aitesam961/electrivity/docs/image_2024-02-22_001135263.png

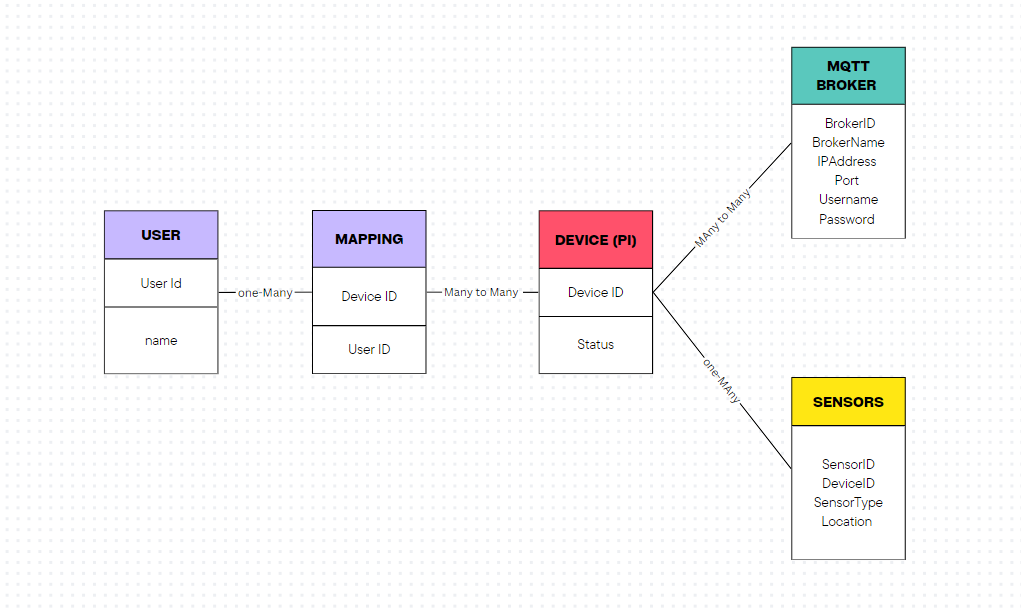
docs/image_2024-02-22_001135263.png
