aitesam961/electrivity/docs/images/image1.jpeg

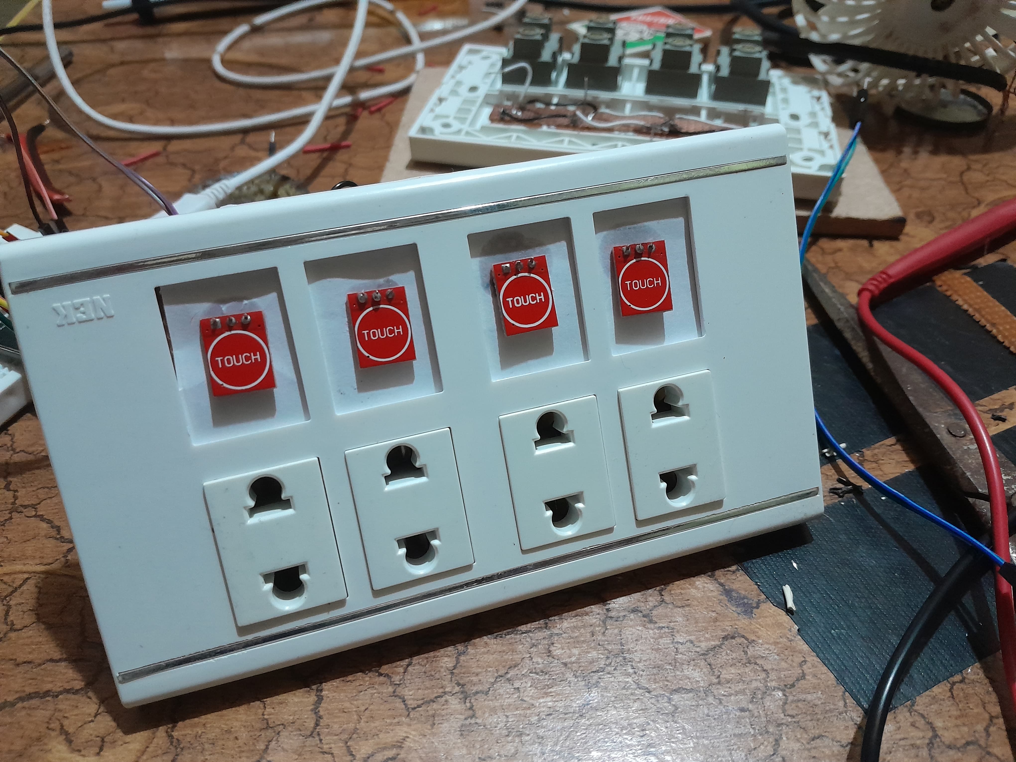
docs/images/image1.jpeg
