aitesam961/electrivity/docs/images/image2.jpeg

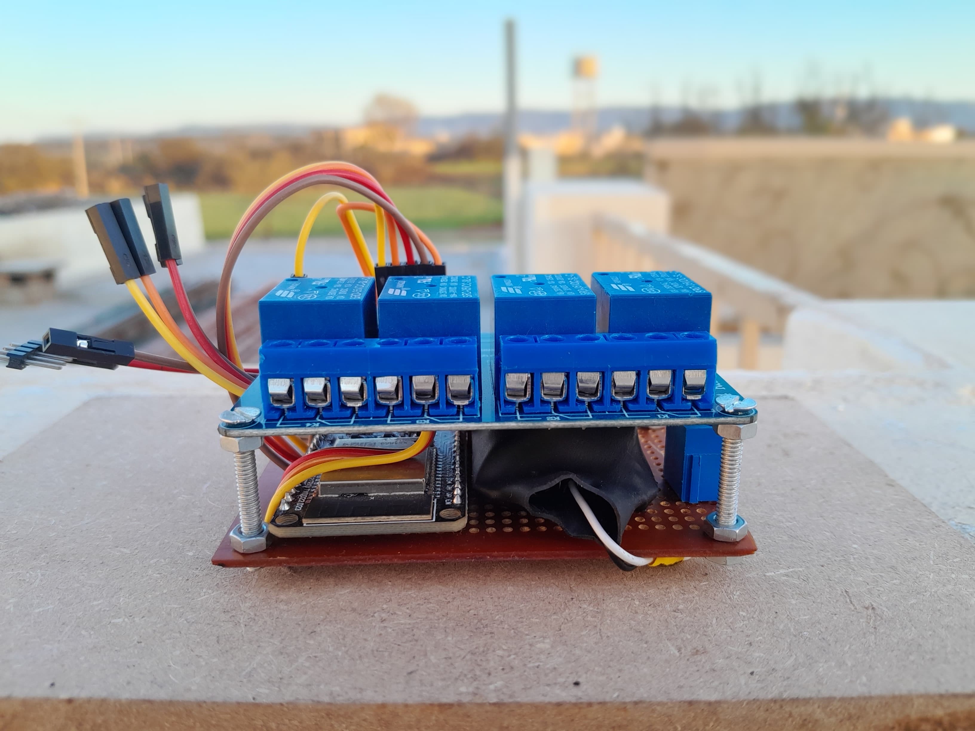
docs/images/image2.jpeg
