aitesam961/electrivity/docs/images/image3.jpeg

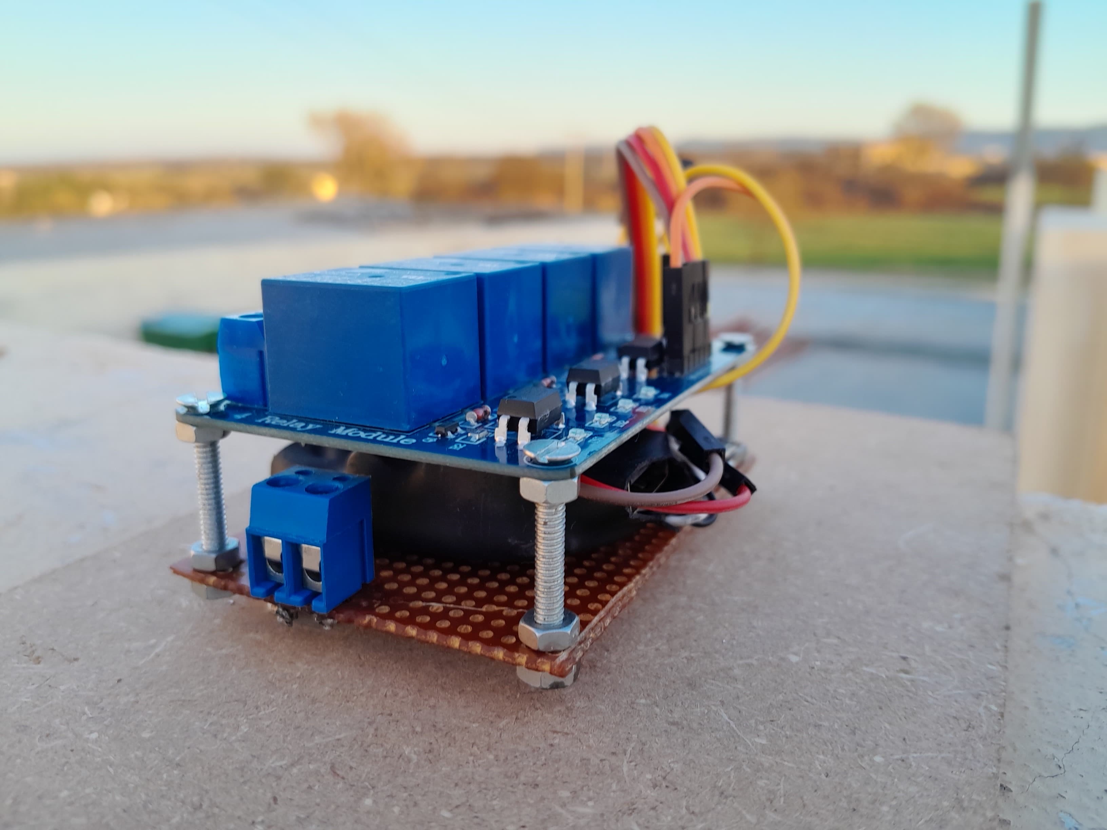
docs/images/image3.jpeg
