aitesam961/electrivity/docs/images/image4.jpeg

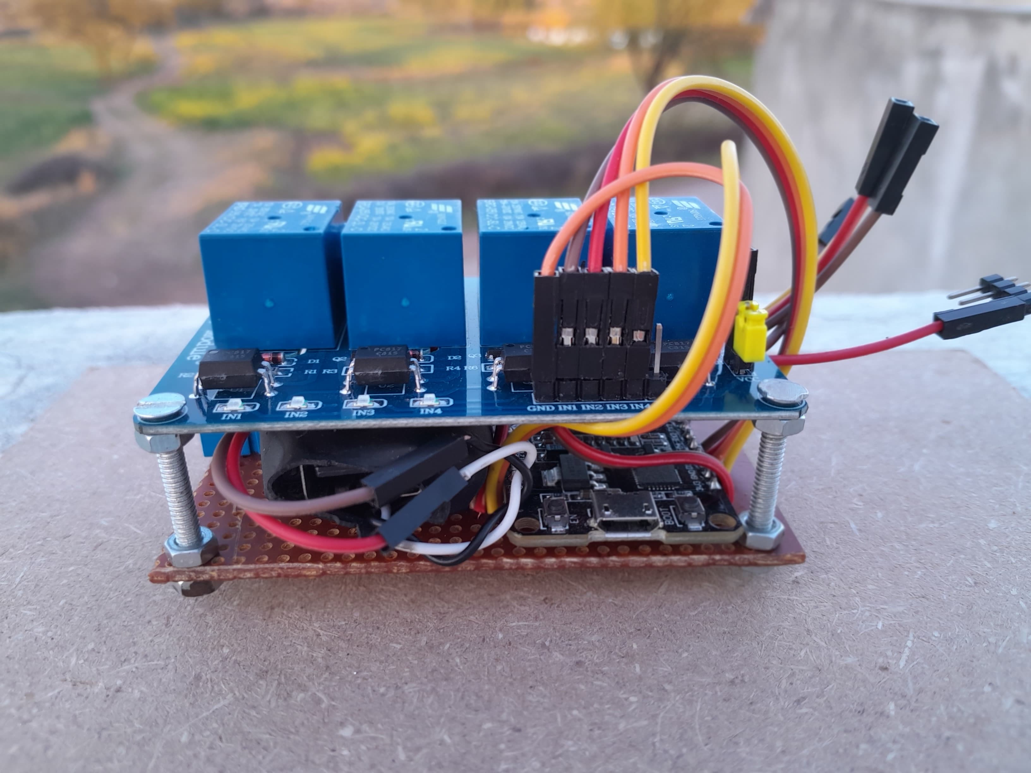
docs/images/image4.jpeg
