aitesam961/electrivity/docs/images/image5.jpeg

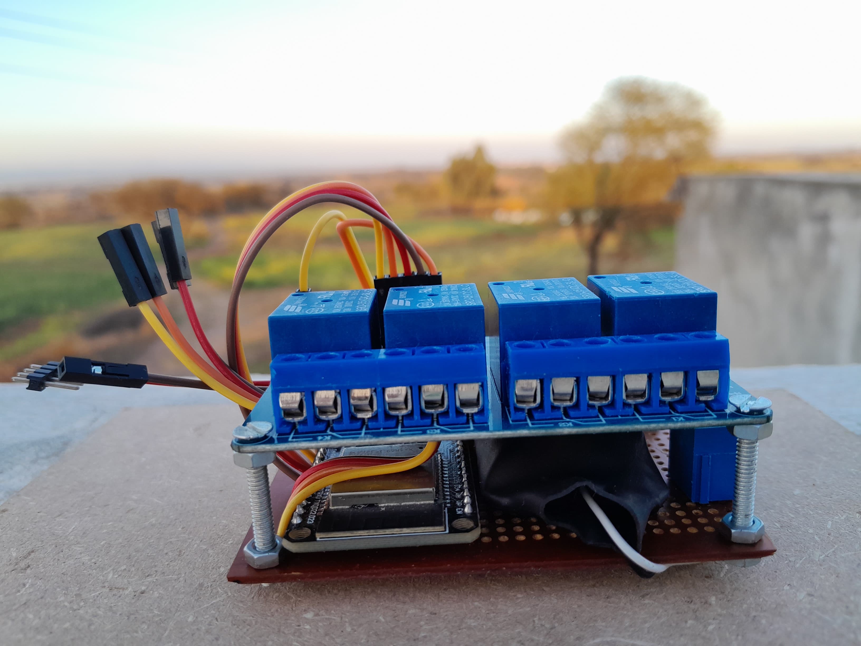
docs/images/image5.jpeg
