aitesam961/electrivity/docs/images/image6.jpeg

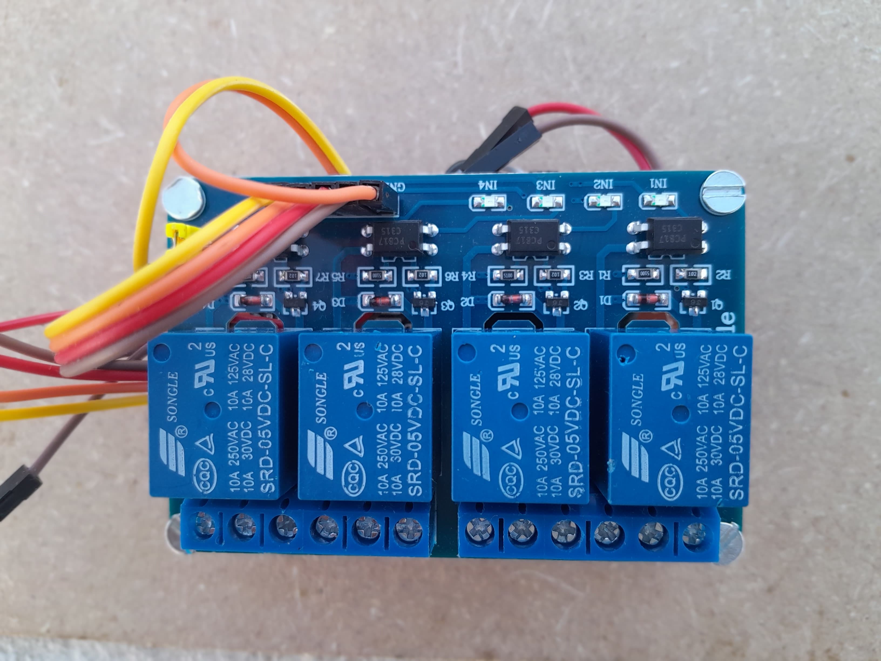
docs/images/image6.jpeg
